yahia-svg/218-DJ-Controller/Schem/218DJ.kicad_sch

## KiCad design Schem/218DJ.kicad_sch (2026-09-21, an earlier design)

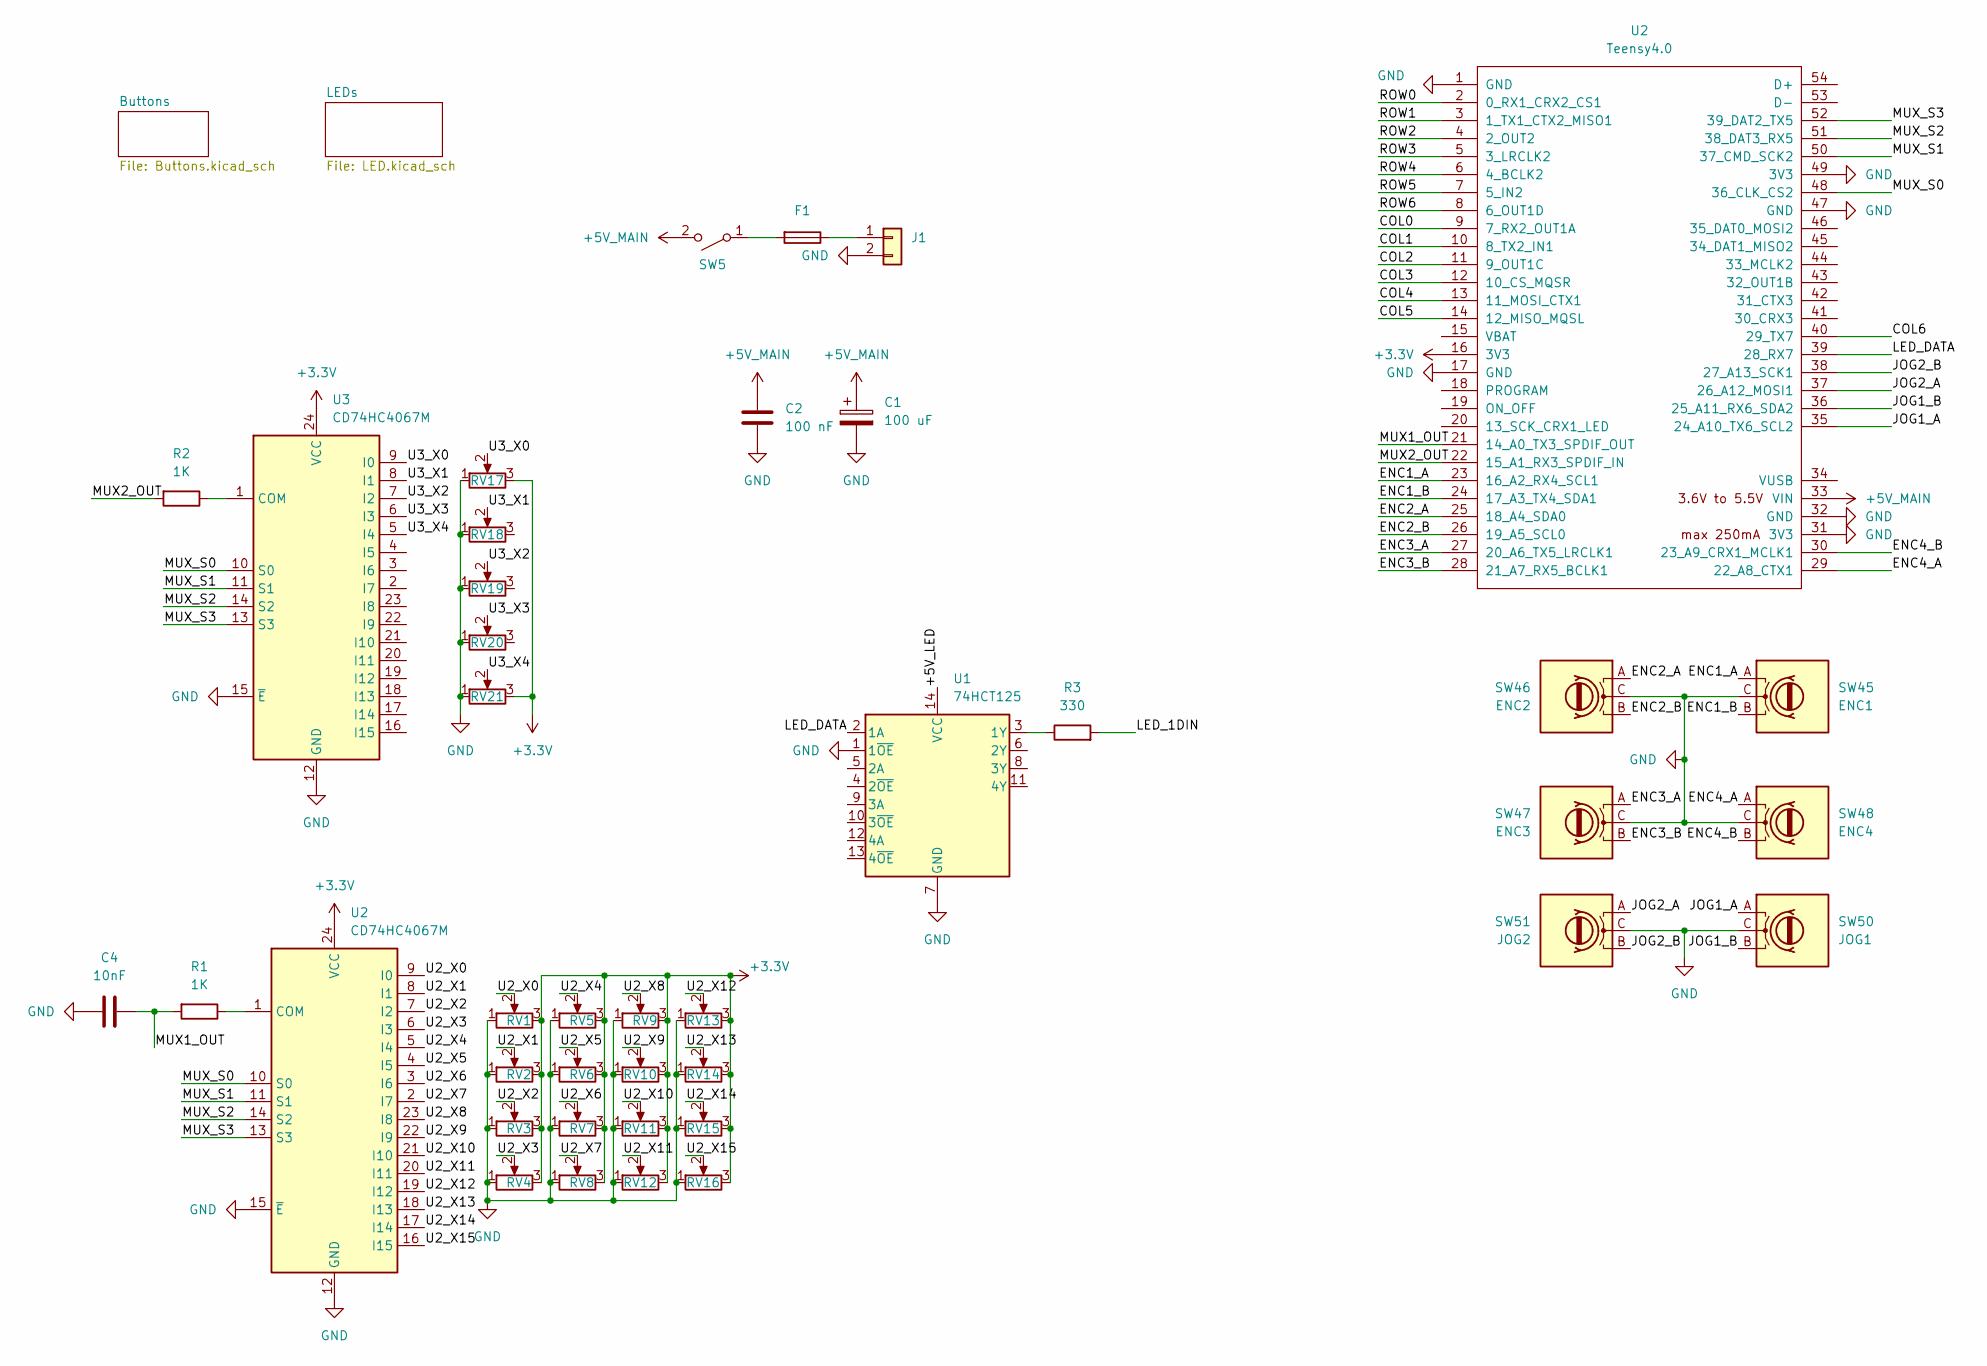
[picture p5: schematic 218DJ.kicad_sch]

Parts:
C1: 100 uF
C2: 100 nF
C4: 10nF
F1: Fuse
J1: 5V_IN
R1, R2: 1K
R3: 330
RV1, RV2, RV3, RV4, RV5, RV6, RV7, RV8, RV9, RV10, RV11, RV12, RV13, RV14, RV15, RV16, RV17, RV18, RV19, RV20, RV21: R_Potentiometer
SW5: SW_SPST
SW45: ENC1
SW46: ENC2
SW47: ENC3
SW48: ENC4
SW50: JOG1
SW51: JOG2
U1: 74HCT125
U2: Teensy4.0
U3: CD74HC4067M; SOIC-24W_7.5x15.4mm_P1.27mm

Connections:
+3.3V: RV1.3, RV2.3, RV3.3, RV4.3, RV5.3, RV6.3, RV7.3, RV8.3, RV9.3, RV10.3, RV11.3, RV12.3, RV13.3, RV14.3, RV15.3, RV16.3, RV17.3, RV21.3, U2.16 (I15), U2.24 (VCC), U3.24 (VCC)
+5V_LED: U1.14 (VCC)
+5V_MAIN: C1.1, C2.1, SW5.2 (B), U2.33 (VIN)
COL0: U2.9 (I0)
COL1: U2.10 (S0)
COL2: U2.11 (S1)
COL3: U2.12 (GND)
COL4: U2.13 (S3)
COL5: U2.14 (S2)
COL6: U2.40 (29_TX7)
ENC1_A: SW45.A, U2.23 (I8)
ENC1_B: SW45.B, U2.24 (VCC)
ENC2_A: SW46.A, U2.25 (18_A4_SDA0)
ENC2_B: SW46.B, U2.26 (19_A5_SCL0)
ENC3_A: SW47.A, U2.27 (20_A6_TX5_LRCLK1)
ENC3_B: SW47.B, U2.28 (21_A7_RX5_BCLK1)
ENC4_A: SW48.A, U2.29 (22_A8_CTX1)
ENC4_B: SW48.B, U2.30 (23_A9_CRX1_MCLK1)
GND: C1.2, C2.2, C4.1, J1.2 (GND), RV1.1, RV2.1, RV3.1, RV4.1, RV5.1, RV6.1, RV7.1, RV8.1, RV9.1, RV10.1, RV11.1, RV12.1, RV13.1, RV14.1, RV15.1, RV16.1, RV17.1, RV18.1, RV19.1, RV20.1, RV21.1, SW45.C, SW46.C, SW47.C, SW48.C, SW50.C, SW51.C, U1.1 (1~OE), U1.7 (GND), U2.1 (COM), U2.12 (GND), U2.15 (~E), U2.17 (I14), U2.31 (3V3), U2.32 (GND), U2.47 (GND), U2.49 (3V3), U3.12 (GND), U3.15 (~E)
JOG1_A: SW50.A, U2.35 (24_A10_TX6_SCL2)
JOG1_B: SW50.B, U2.36 (25_A11_RX6_SDA2)
JOG2_A: SW51.A, U2.37 (26_A12_MOSI1)
JOG2_B: SW51.B, U2.38 (27_A13_SCK1)
LED_1DIN: R3.2
LED_DATA: U1.2 (1A), U2.39 (28_RX7)
MUX1_OUT: C4.2, R1.2, U2.21 (I10)
MUX2_OUT: R2.2, U2.22 (I9)
MUX_S0: U2.10 (S0), U2.48 (36_CLK_CS2), U3.10 (S0)
MUX_S1: U2.11 (S1), U2.50 (37_CMD_SCK2), U3.11 (S1)
MUX_S2: U2.14 (S2), U2.51 (38_DAT3_RX5), U3.14 (S2)
MUX_S3: U2.13 (S3), U2.52 (39_DAT2_TX5), U3.13 (S3)
unnamed: F1.1, J1.1 (+5V)
unnamed: F1.2, SW5.1 (A)
unnamed: R1.1, U2.1 (COM)
unnamed: R2.1, U3.1 (COM)
unnamed: R3.1, U1.3 (1Y)
ROW0: U2.2 (I7)
ROW1: U2.3 (I6)
ROW2: U2.4 (I5)
ROW3: U2.5 (I4)
ROW4: U2.6 (I3)
ROW5: U2.7 (I2)
ROW6: U2.8 (I1)
U2_X0: RV1.2, U2.9 (I0)
U2_X1: RV2.2, U2.8 (I1)
U2_X2: RV3.2, U2.7 (I2)
U2_X3: RV4.2, U2.6 (I3)
U2_X4: RV5.2, U2.5 (I4)
U2_X5: RV6.2, U2.4 (I5)
U2_X6: RV7.2, U2.3 (I6)
U2_X7: RV8.2, U2.2 (I7)
U2_X8: RV9.2, U2.23 (I8)
U2_X9: RV10.2, U2.22 (I9)
U2_X10: RV11.2, U2.21 (I10)
U2_X11: RV12.2, U2.20 (I11)
U2_X12: RV13.2, U2.19 (I12)
U2_X13: RV14.2, U2.18 (I13)
U2_X14: RV15.2, U2.17 (I14)
U2_X15: RV16.2, U2.16 (I15)
U3_X0: RV17.2, U3.9 (I0)
U3_X1: RV18.2, U3.8 (I1)
U3_X2: RV19.2, U3.7 (I2)
U3_X3: RV20.2, U3.6 (I3)
U3_X4: RV21.2, U3.5 (I4)
