yahia-svg/218-DJ-Controller/Schem/Buttons.kicad_sch

## KiCad design Schem/Buttons.kicad_sch (2026-09-21, an earlier design)

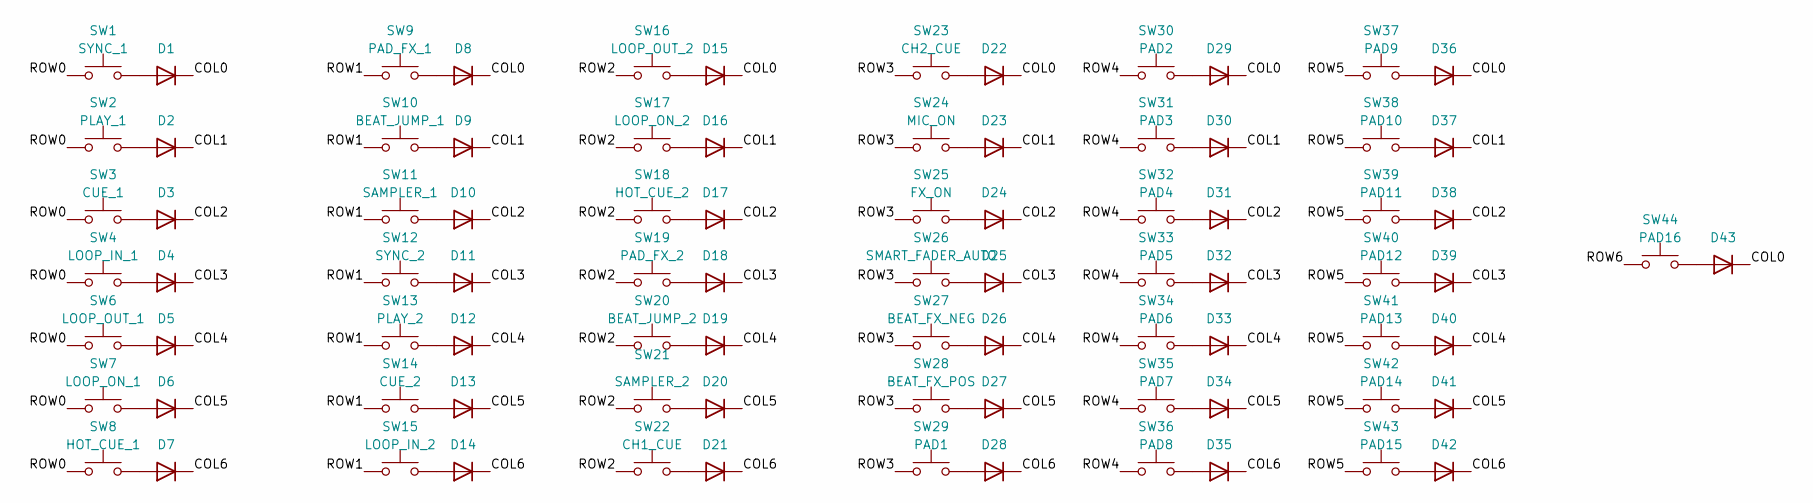
[picture p6: schematic Buttons.kicad_sch]

Parts:
D1, D2, D3, D4, D5, D6, D7, D8, D9, D10, D11, D12, D13, D14, D15, D16, D17, D18, D19, D20, D21, D22, D23, D24, D25, D26, D27, D28, D29, D30, D31, D32, D33, D34, D35, D36, D37, D38, D39, D40, D41, D42, D43: (no value)
SW1: SYNC_1
SW2: PLAY_1
SW3: CUE_1
SW4: LOOP_IN_1
SW6: LOOP_OUT_1
SW7: LOOP_ON_1
SW8: HOT_CUE_1
SW9: PAD_FX_1
SW10: BEAT_JUMP_1
SW11: SAMPLER_1
SW12: SYNC_2
SW13: PLAY_2
SW14: CUE_2
SW15: LOOP_IN_2
SW16: LOOP_OUT_2
SW17: LOOP_ON_2
SW18: HOT_CUE_2
SW19: PAD_FX_2
SW20: BEAT_JUMP_2
SW21: SAMPLER_2
SW22: CH1_CUE
SW23: CH2_CUE
SW24: MIC_ON
SW25: FX_ON
SW26: SMART_FADER_AUTO
SW27: BEAT_FX_NEG
SW28: BEAT_FX_POS
SW29: PAD1
SW30: PAD2
SW31: PAD3
SW32: PAD4
SW33: PAD5
SW34: PAD6
SW35: PAD7
SW36: PAD8
SW37: PAD9
SW38: PAD10
SW39: PAD11
SW40: PAD12
SW41: PAD13
SW42: PAD14
SW43: PAD15
SW44: PAD16

Connections:
COL0: D1.1 (K), D8.1 (K), D15.1 (K), D22.1 (K), D29.1 (K), D36.1 (K), D43.1 (K)
COL1: D2.1 (K), D9.1 (K), D16.1 (K), D23.1 (K), D30.1 (K), D37.1 (K)
COL2: D3.1 (K), D10.1 (K), D17.1 (K), D24.1 (K), D31.1 (K), D38.1 (K)
COL3: D4.1 (K), D11.1 (K), D18.1 (K), D25.1 (K), D32.1 (K), D39.1 (K)
COL4: D5.1 (K), D12.1 (K), D19.1 (K), D26.1 (K), D33.1 (K), D40.1 (K)
COL5: D6.1 (K), D13.1 (K), D20.1 (K), D27.1 (K), D34.1 (K), D41.1 (K)
COL6: D7.1 (K), D14.1 (K), D21.1 (K), D28.1 (K), D35.1 (K), D42.1 (K)
unnamed: D1.2 (A), SW1.2
unnamed: D2.2 (A), SW2.2
unnamed: D3.2 (A), SW3.2
unnamed: D4.2 (A), SW4.2
unnamed: D5.2 (A), SW6.2
unnamed: D6.2 (A), SW7.2
unnamed: D7.2 (A), SW8.2
unnamed: D8.2 (A), SW9.2
unnamed: D9.2 (A), SW10.2
unnamed: D10.2 (A), SW11.2
unnamed: D11.2 (A), SW12.2
unnamed: D12.2 (A), SW13.2
unnamed: D13.2 (A), SW14.2
unnamed: D14.2 (A), SW15.2
unnamed: D15.2 (A), SW16.2
unnamed: D16.2 (A), SW17.2
unnamed: D17.2 (A), SW18.2
unnamed: D18.2 (A), SW19.2
unnamed: D19.2 (A), SW20.2
unnamed: D20.2 (A), SW21.2
unnamed: D21.2 (A), SW22.2
unnamed: D22.2 (A), SW23.2
unnamed: D23.2 (A), SW24.2
unnamed: D24.2 (A), SW25.2
unnamed: D25.2 (A), SW26.2
unnamed: D26.2 (A), SW27.2
unnamed: D27.2 (A), SW28.2
unnamed: D28.2 (A), SW29.2
unnamed: D29.2 (A), SW30.2
unnamed: D30.2 (A), SW31.2
unnamed: D31.2 (A), SW32.2
unnamed: D32.2 (A), SW33.2
unnamed: D33.2 (A), SW34.2
unnamed: D34.2 (A), SW35.2
unnamed: D35.2 (A), SW36.2
unnamed: D36.2 (A), SW37.2
unnamed: D37.2 (A), SW38.2
unnamed: D38.2 (A), SW39.2
unnamed: D39.2 (A), SW40.2
unnamed: D40.2 (A), SW41.2
unnamed: D41.2 (A), SW42.2
unnamed: D42.2 (A), SW43.2
unnamed: D43.2 (A), SW44.2
ROW0: SW1.1, SW2.1, SW3.1, SW4.1, SW6.1, SW7.1, SW8.1
ROW1: SW9.1, SW10.1, SW11.1, SW12.1, SW13.1, SW14.1, SW15.1
ROW2: SW16.1, SW17.1, SW18.1, SW19.1, SW20.1, SW21.1, SW22.1
ROW3: SW23.1, SW24.1, SW25.1, SW26.1, SW27.1, SW28.1, SW29.1
ROW4: SW30.1, SW31.1, SW32.1, SW33.1, SW34.1, SW35.1, SW36.1
ROW5: SW37.1, SW38.1, SW39.1, SW40.1, SW41.1, SW42.1, SW43.1
ROW6: SW44.1
