yahia-svg/218-DJ-Controller/Schem/LED.kicad_sch

## KiCad design Schem/LED.kicad_sch (2026-09-21, an earlier design)

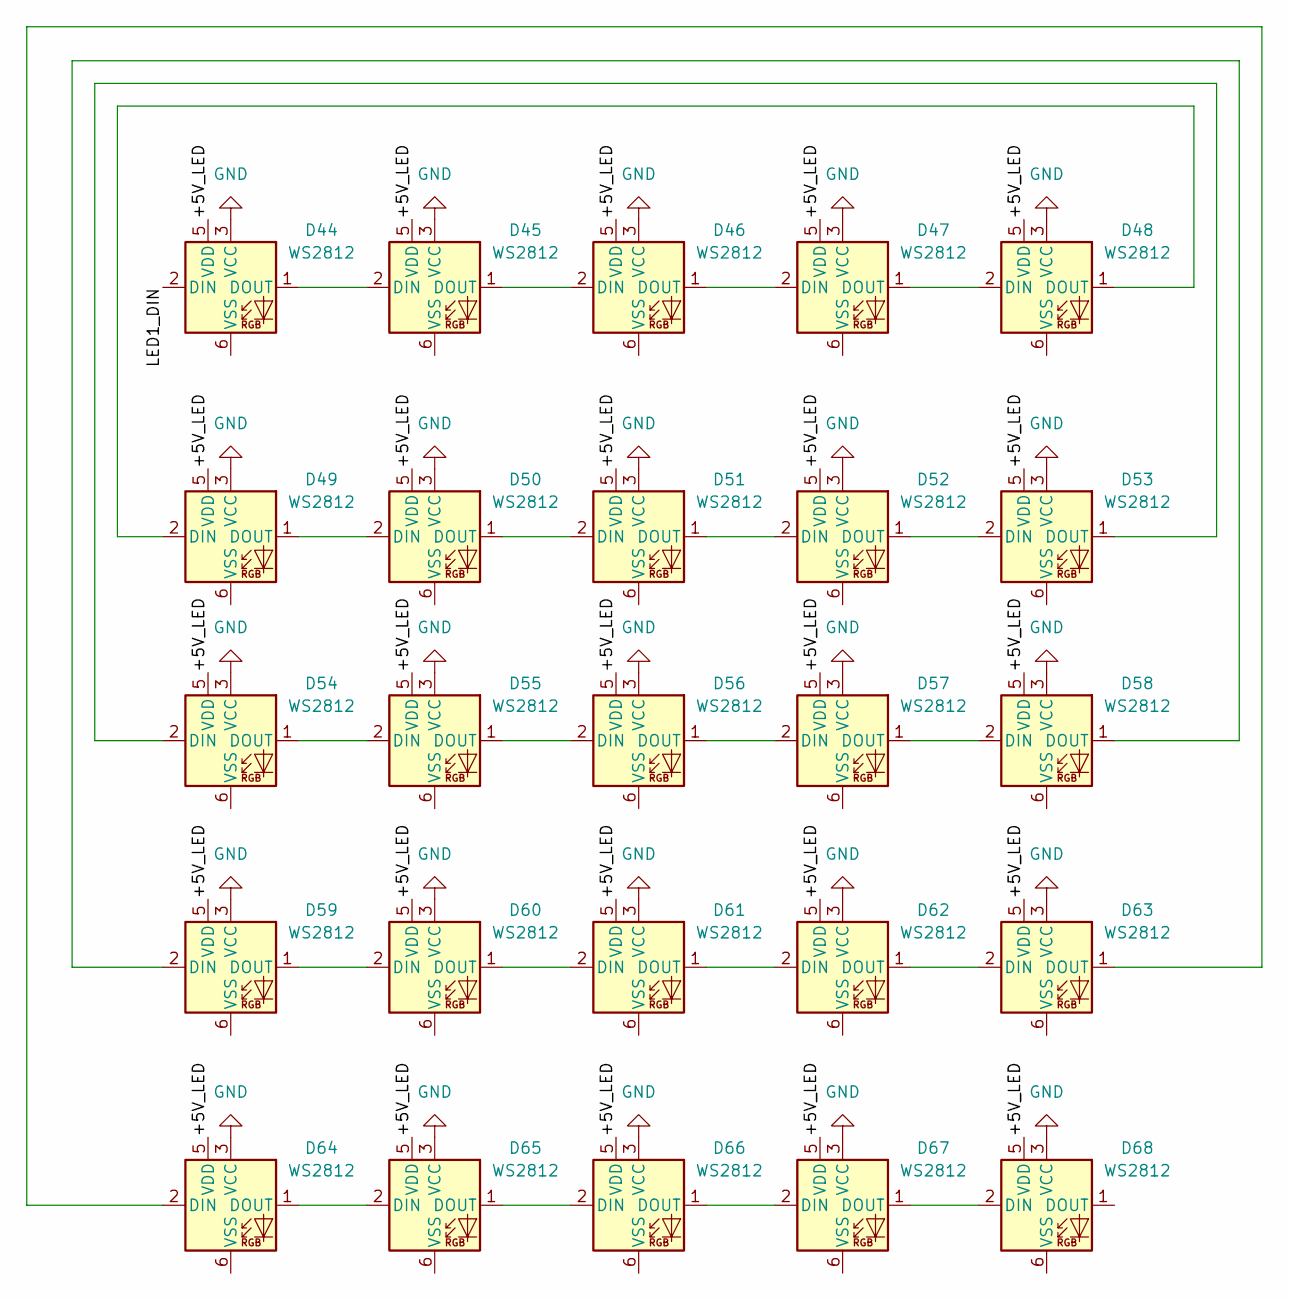
[picture p7: schematic LED.kicad_sch]

Parts:
D44, D45, D46, D47, D48, D49, D50, D51, D52, D53, D54, D55, D56, D57, D58, D59, D60, D61, D62, D63, D64, D65, D66, D67, D68: WS2812; LED_WS2812_PLCC6_5.0x5.0mm_P1.6mm

Connections:
+5V_LED: D44.5 (VDD), D45.5 (VDD), D46.5 (VDD), D47.5 (VDD), D48.5 (VDD), D49.5 (VDD), D50.5 (VDD), D51.5 (VDD), D52.5 (VDD), D53.5 (VDD), D54.5 (VDD), D55.5 (VDD), D56.5 (VDD), D57.5 (VDD), D58.5 (VDD), D59.5 (VDD), D60.5 (VDD), D61.5 (VDD), D62.5 (VDD), D63.5 (VDD), D64.5 (VDD), D65.5 (VDD), D66.5 (VDD), D67.5 (VDD), D68.5 (VDD)
GND: D44.3 (VCC), D45.3 (VCC), D46.3 (VCC), D47.3 (VCC), D48.3 (VCC), D49.3 (VCC), D50.3 (VCC), D51.3 (VCC), D52.3 (VCC), D53.3 (VCC), D54.3 (VCC), D55.3 (VCC), D56.3 (VCC), D57.3 (VCC), D58.3 (VCC), D59.3 (VCC), D60.3 (VCC), D61.3 (VCC), D62.3 (VCC), D63.3 (VCC), D64.3 (VCC), D65.3 (VCC), D66.3 (VCC), D67.3 (VCC), D68.3 (VCC)
LED1_DIN: D44.2 (DIN)
unnamed: D44.1 (DOUT), D45.2 (DIN)
unnamed: D45.1 (DOUT), D46.2 (DIN)
unnamed: D46.1 (DOUT), D47.2 (DIN)
unnamed: D47.1 (DOUT), D48.2 (DIN)
unnamed: D48.1 (DOUT), D49.2 (DIN)
unnamed: D49.1 (DOUT), D50.2 (DIN)
unnamed: D50.1 (DOUT), D51.2 (DIN)
unnamed: D51.1 (DOUT), D52.2 (DIN)
unnamed: D52.1 (DOUT), D53.2 (DIN)
unnamed: D53.1 (DOUT), D54.2 (DIN)
unnamed: D54.1 (DOUT), D55.2 (DIN)
unnamed: D55.1 (DOUT), D56.2 (DIN)
unnamed: D56.1 (DOUT), D57.2 (DIN)
unnamed: D57.1 (DOUT), D58.2 (DIN)
unnamed: D58.1 (DOUT), D59.2 (DIN)
unnamed: D59.1 (DOUT), D60.2 (DIN)
unnamed: D60.1 (DOUT), D61.2 (DIN)
unnamed: D61.1 (DOUT), D62.2 (DIN)
unnamed: D62.1 (DOUT), D63.2 (DIN)
unnamed: D63.1 (DOUT), D64.2 (DIN)
unnamed: D64.1 (DOUT), D65.2 (DIN)
unnamed: D65.1 (DOUT), D66.2 (DIN)
unnamed: D66.1 (DOUT), D67.2 (DIN)
unnamed: D67.1 (DOUT), D68.2 (DIN)
